cwahlmann/vz200-remake/3d-model/screenshots/monitor-v1_1.png

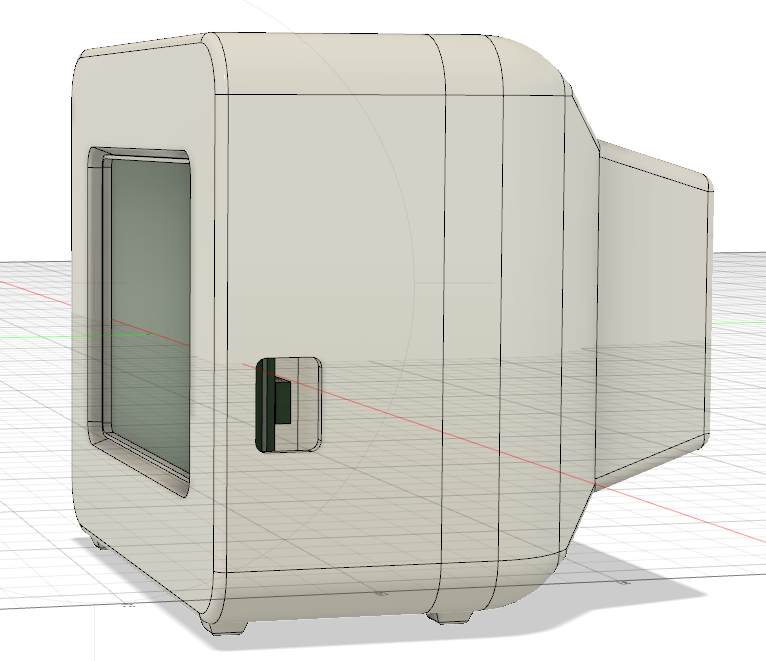
3d-model/screenshots/monitor-v1_1.png
