cwahlmann/vz200-remake/3d-model/screenshots/monitor-v1_2.png

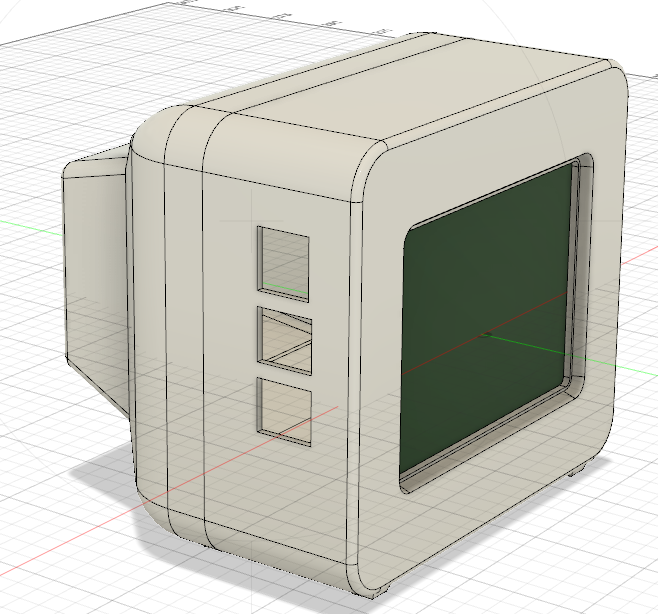
3d-model/screenshots/monitor-v1_2.png
