cwahlmann/vz200-remake/3d-model/screenshots/monitor-v1_3.png

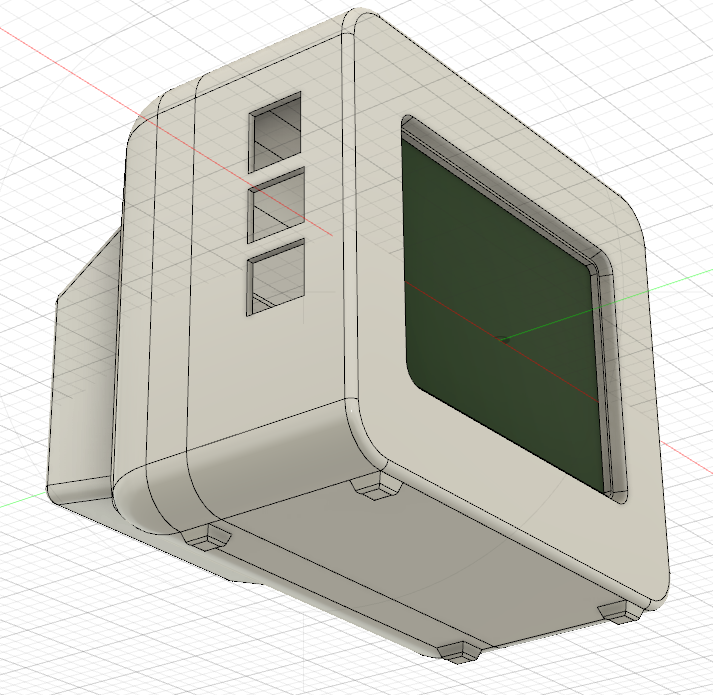
3d-model/screenshots/monitor-v1_3.png
