cwahlmann/vz200-remake/3d-model/screenshots/monitor-v2_5.png

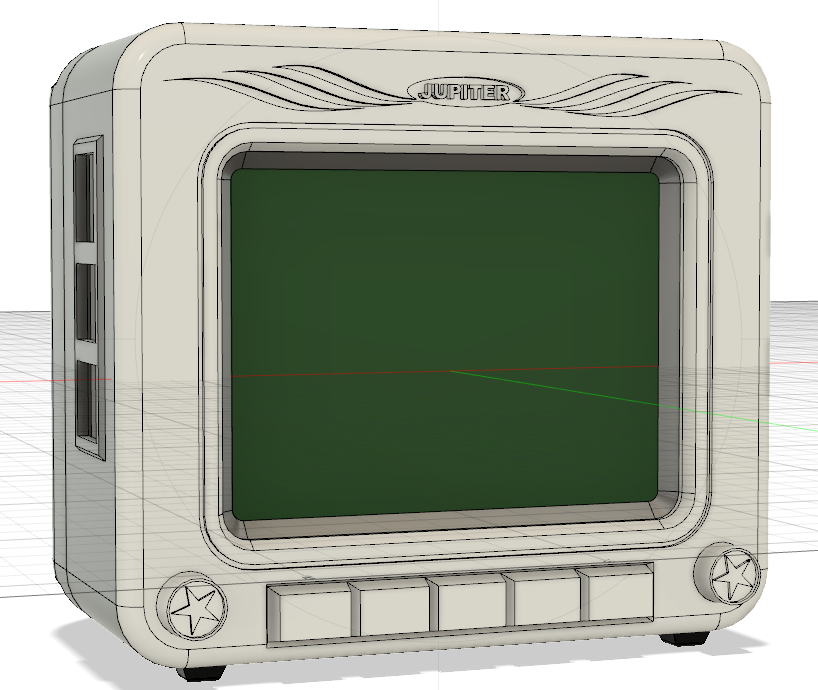
3d-model/screenshots/monitor-v2_5.png
