cwahlmann/vz200-remake/3d-model/screenshots/VZ-Fusion-0.3.png

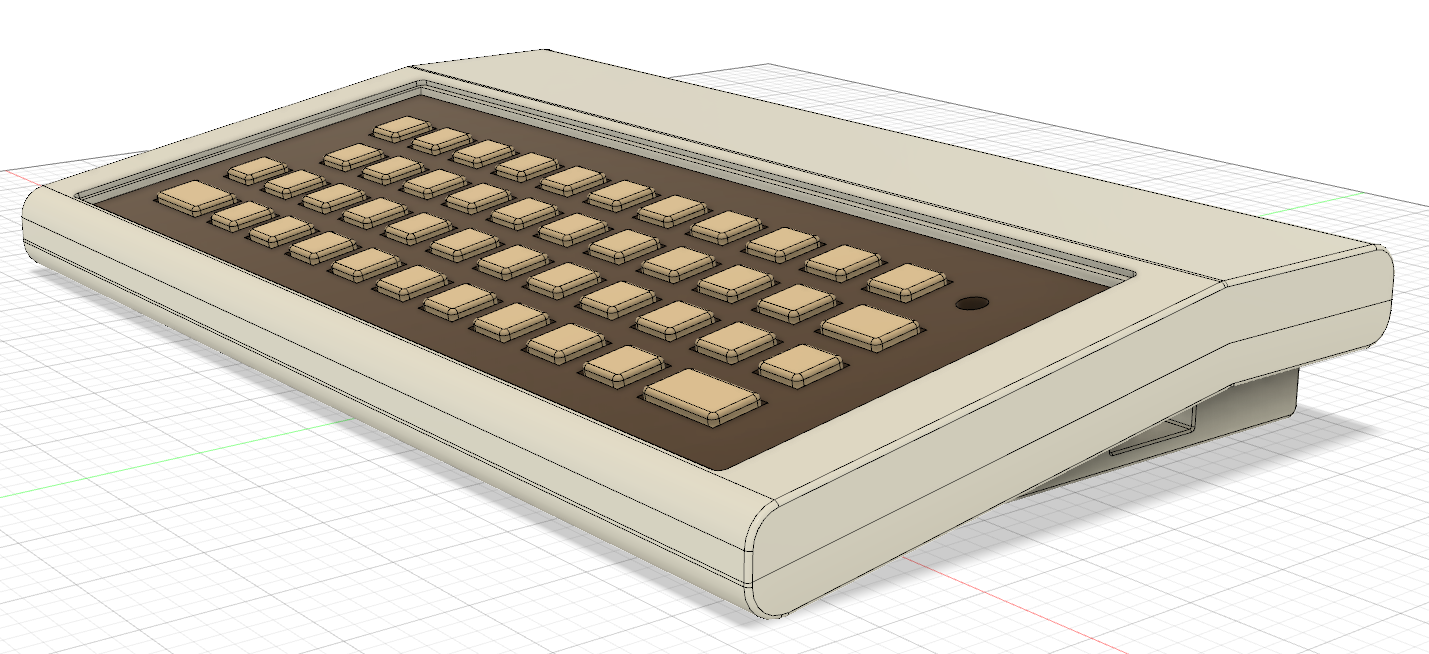
3d-model/screenshots/VZ-Fusion-0.3.png
