cwahlmann/vz200-remake/3d-model/screenshots/VZ-Fusion-0.5b.png

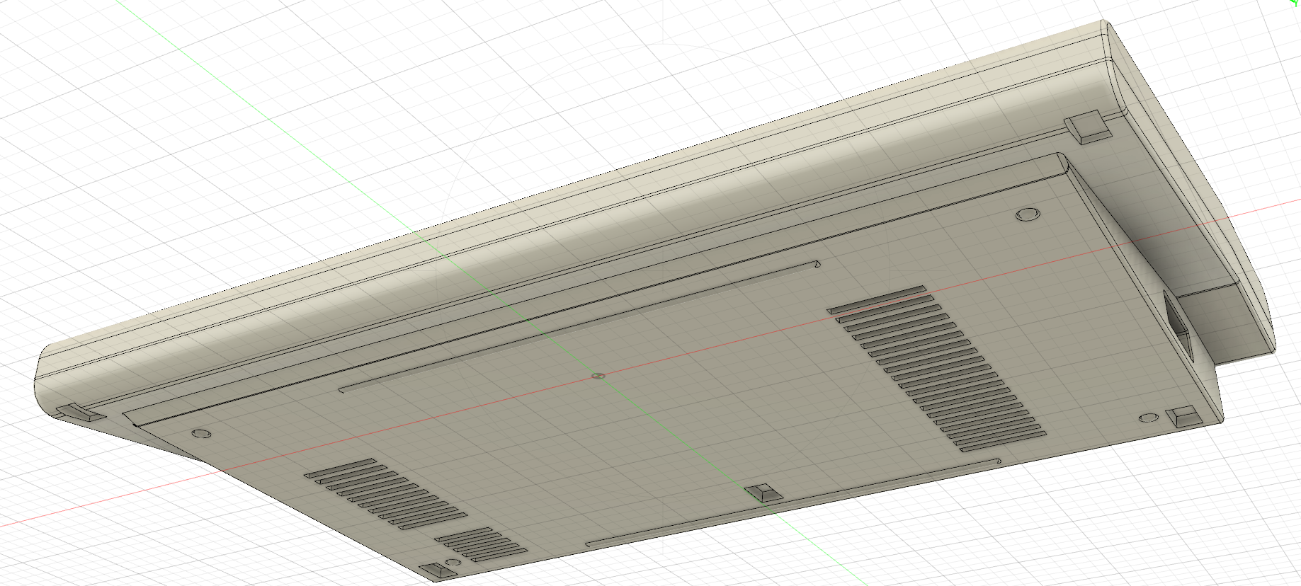
3d-model/screenshots/VZ-Fusion-0.5b.png
