cwahlmann/vz200-remake/3d-model/screenshots/VZ-Fusion-0.5c.png

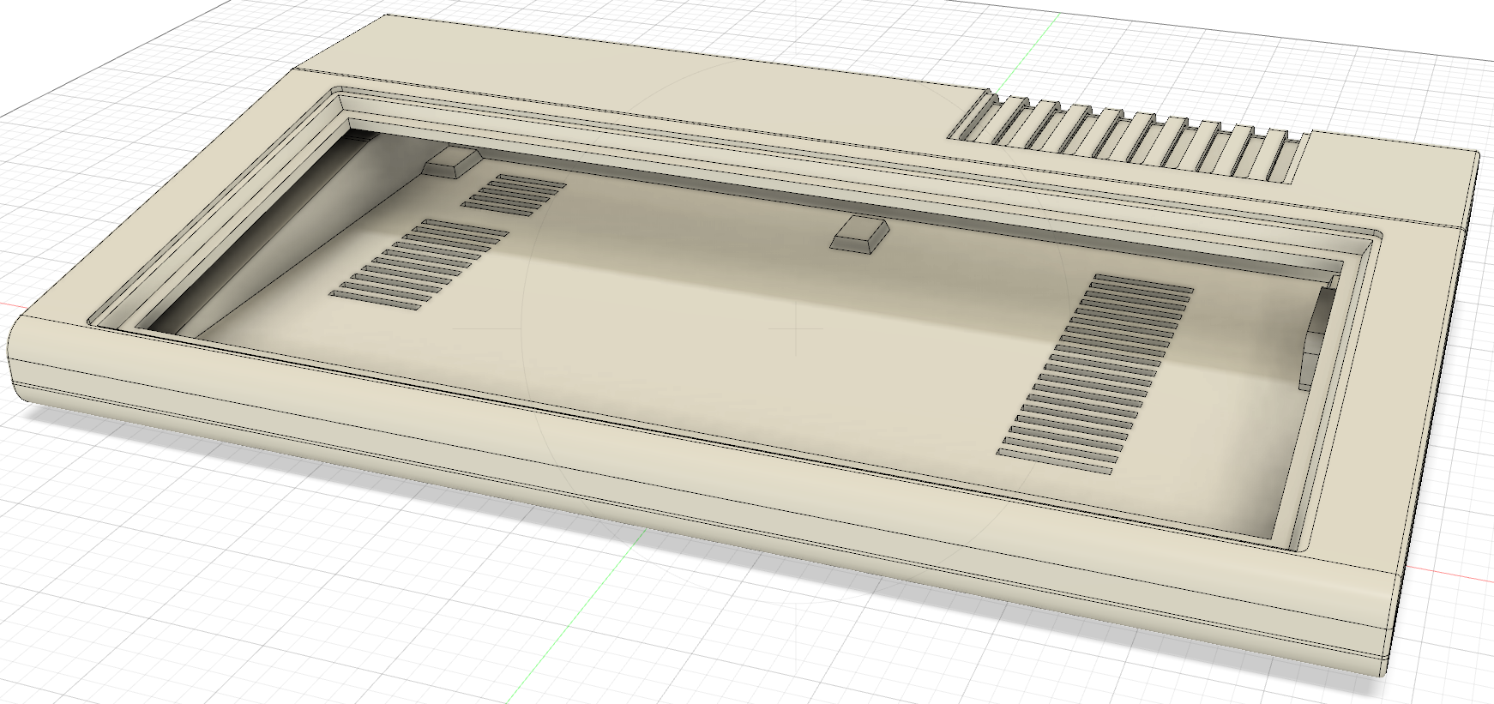
3d-model/screenshots/VZ-Fusion-0.5c.png
