cwahlmann/vz200-remake/3d-model/screenshots/VZ-Fusion-v3-Oben-hinten.png

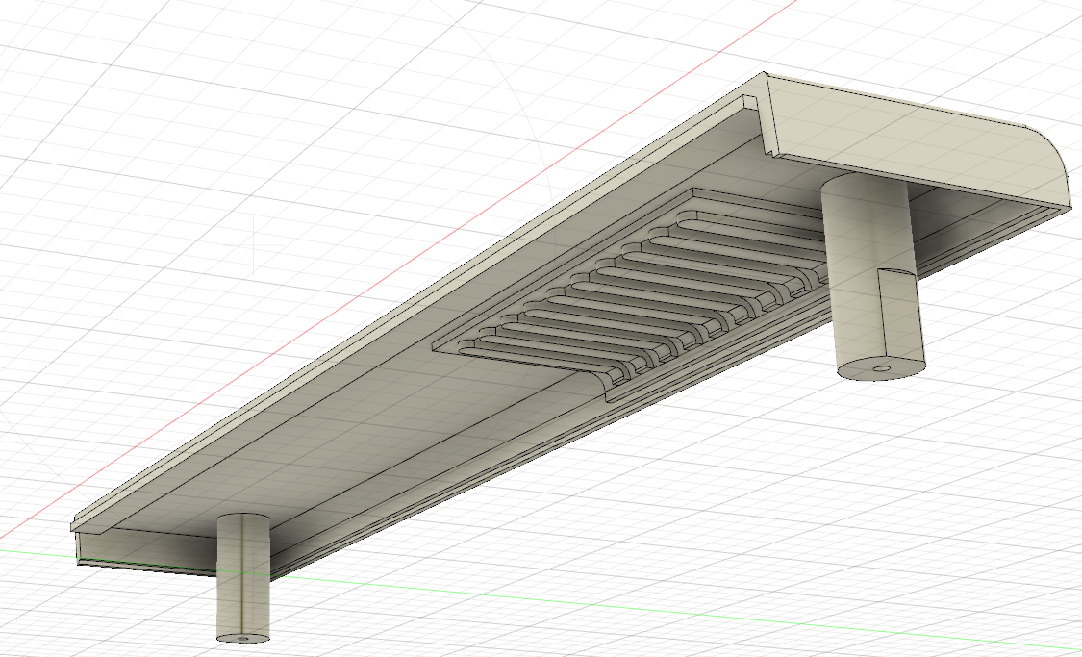
3d-model/screenshots/VZ-Fusion-v3-Oben-hinten.png
