cwahlmann/vz200-remake/3d-model/screenshots/VZ-Fusion-v3-Tastatur-Halterungen-1.png

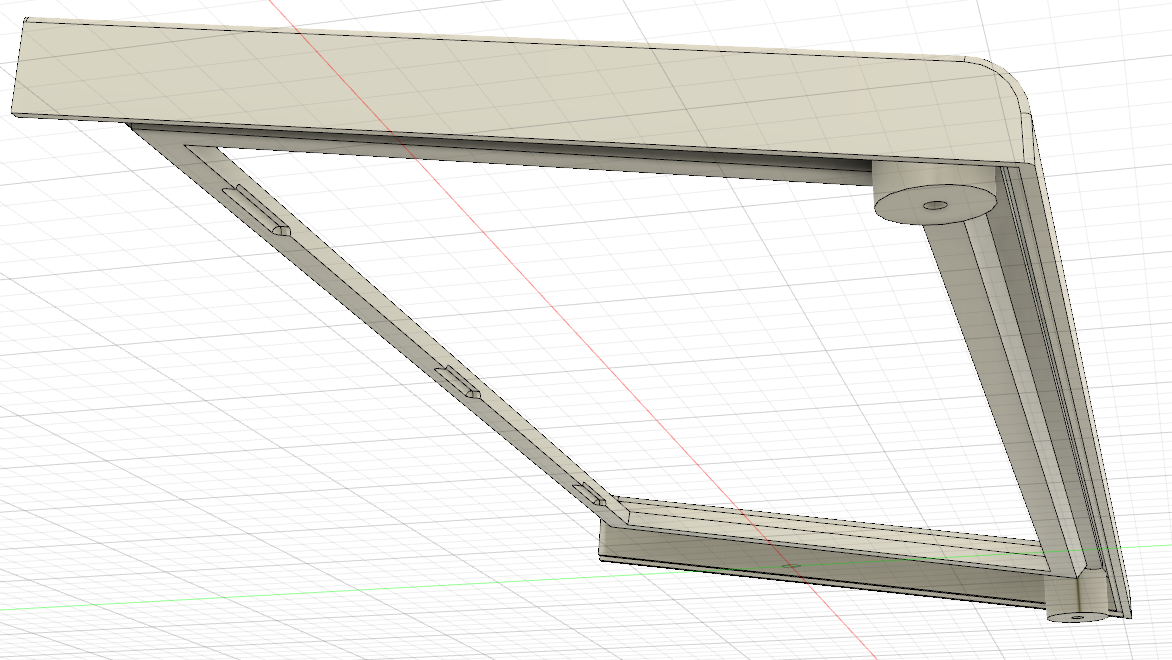
3d-model/screenshots/VZ-Fusion-v3-Tastatur-Halterungen-1.png
