cwahlmann/vz200-remake/3d-model/screenshots/VZ-Fusion-v3-Tastatur-Halterungen-3.png

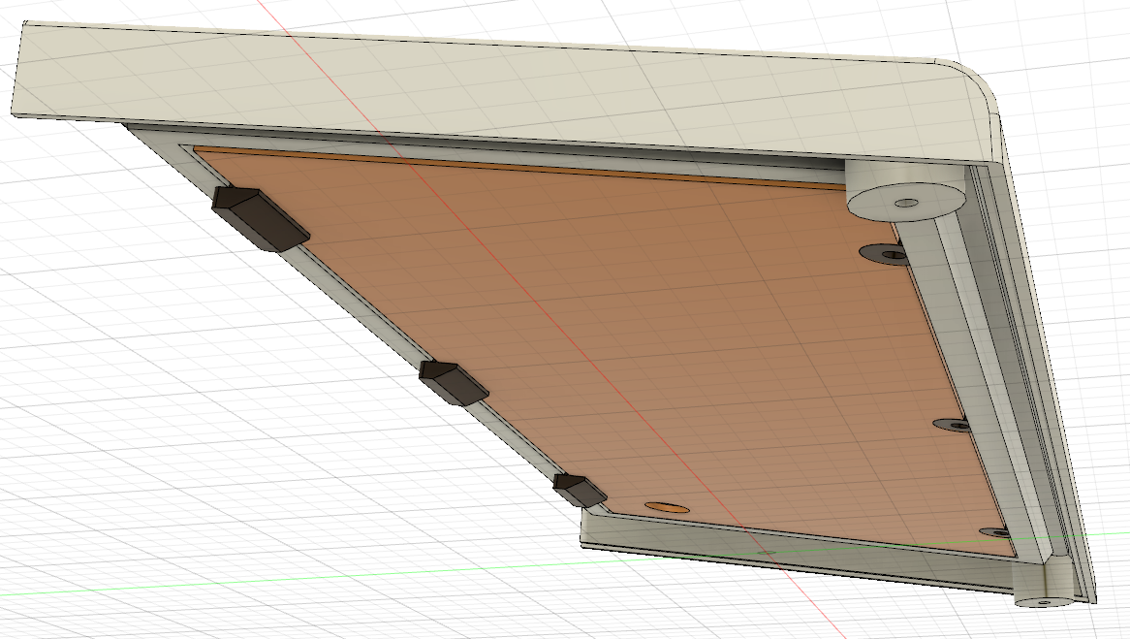
3d-model/screenshots/VZ-Fusion-v3-Tastatur-Halterungen-3.png
