cwahlmann/vz200-remake/audio/audio_schaltplan.png

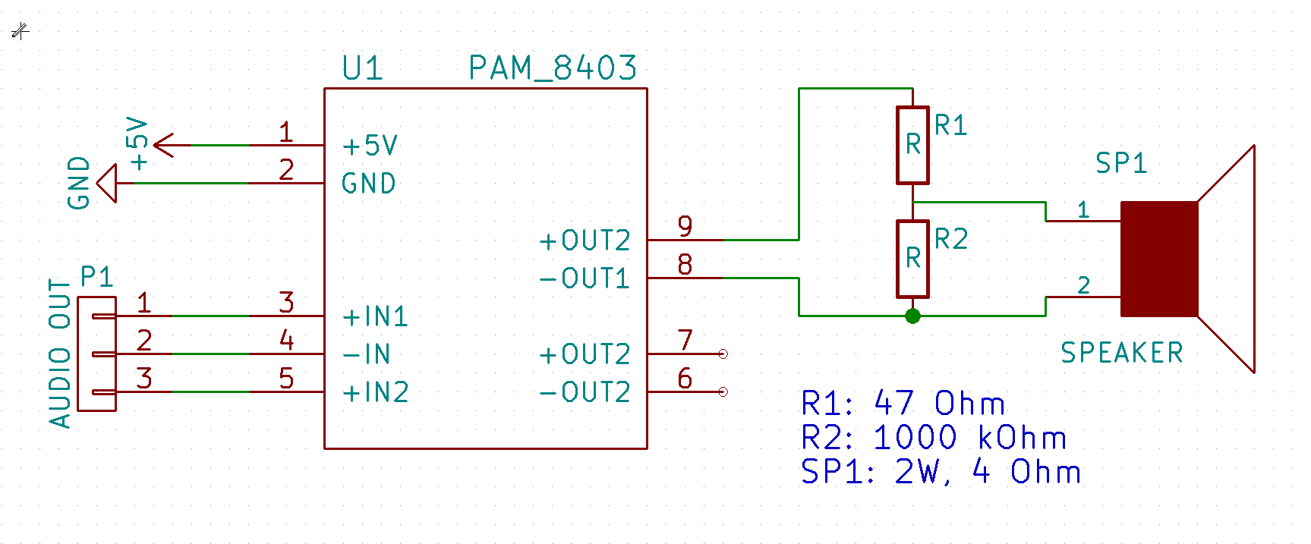
audio/audio_schaltplan.png
