cwahlmann/vz200-remake/images/3d_druck_1.jpg

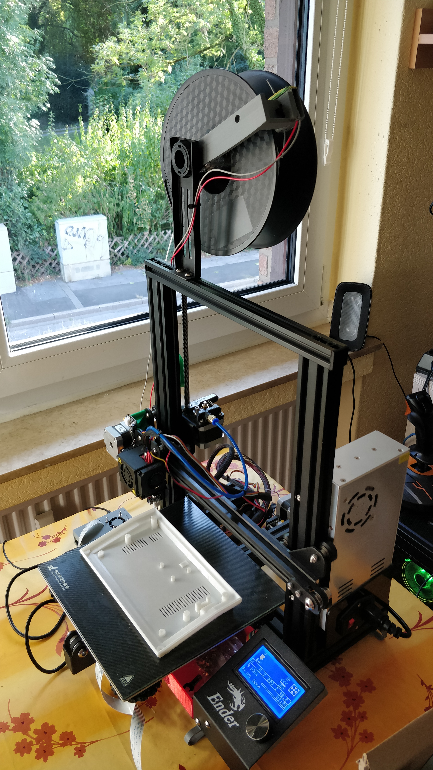
images/3d_druck_1.jpg
