cwahlmann/vz200-remake/images/3d_druck_2.jpg

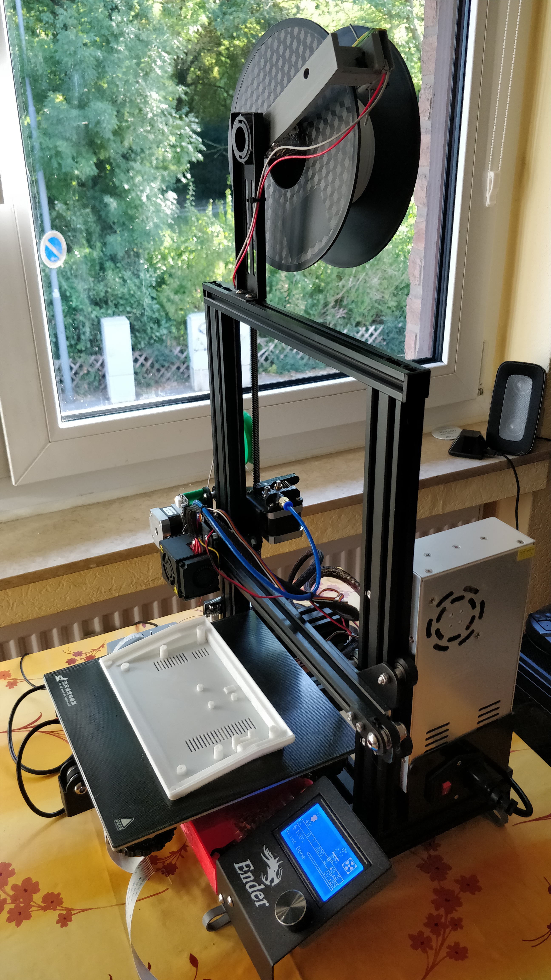
images/3d_druck_2.jpg
