cwahlmann/vz200-remake/images/img_chassis_20_platine_reset.jpg

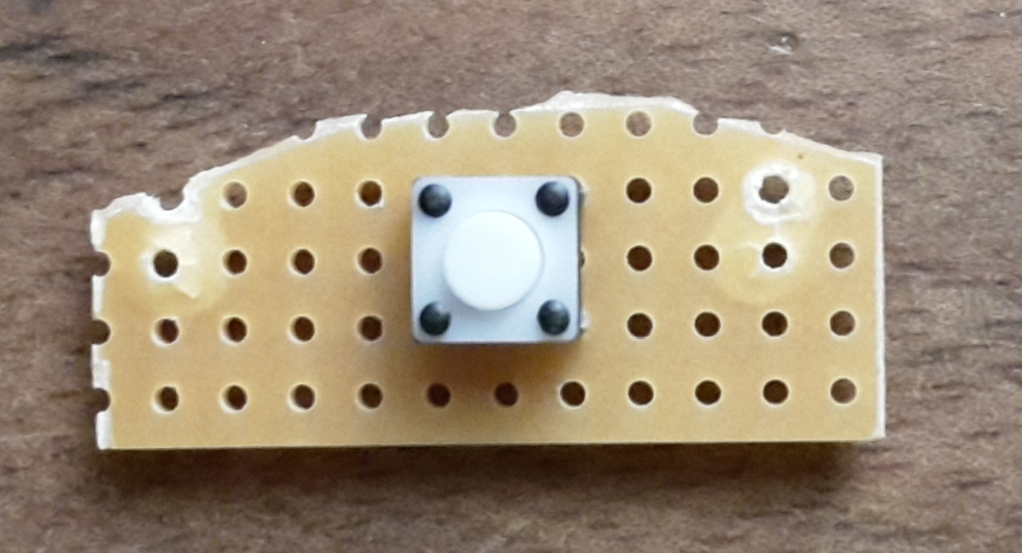
images/img_chassis_20_platine_reset.jpg
