cwahlmann/vz200-remake/images/img_chassis_23_platine_reset.jpg

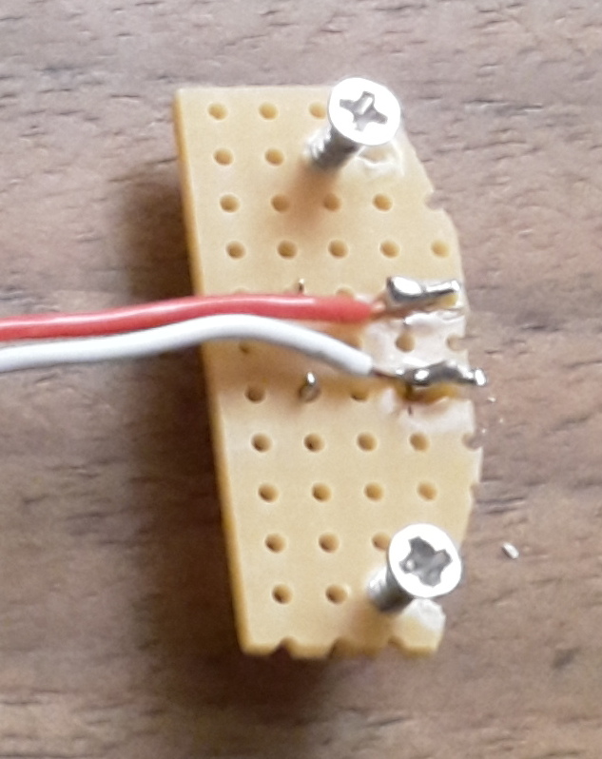
images/img_chassis_23_platine_reset.jpg
