cwahlmann/vz200-remake/images/img_monitor_15_raspberry_tft_einbau.jpg

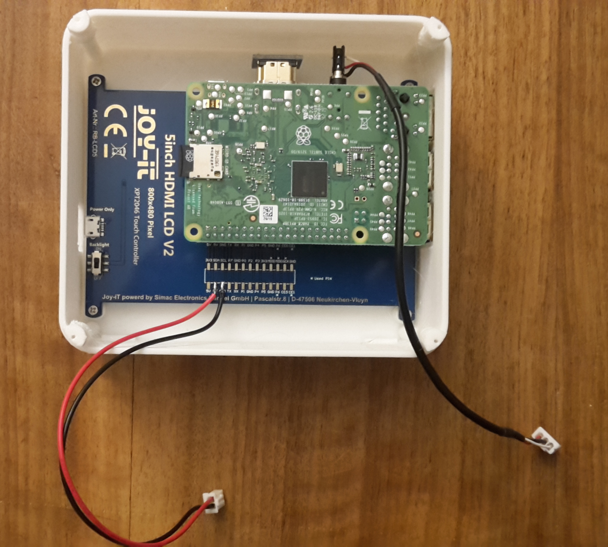
images/img_monitor_15_raspberry_tft_einbau.jpg
