cwahlmann/vz200-remake/images/img_monitor_17_verkabelung_gesamt_2.jpg

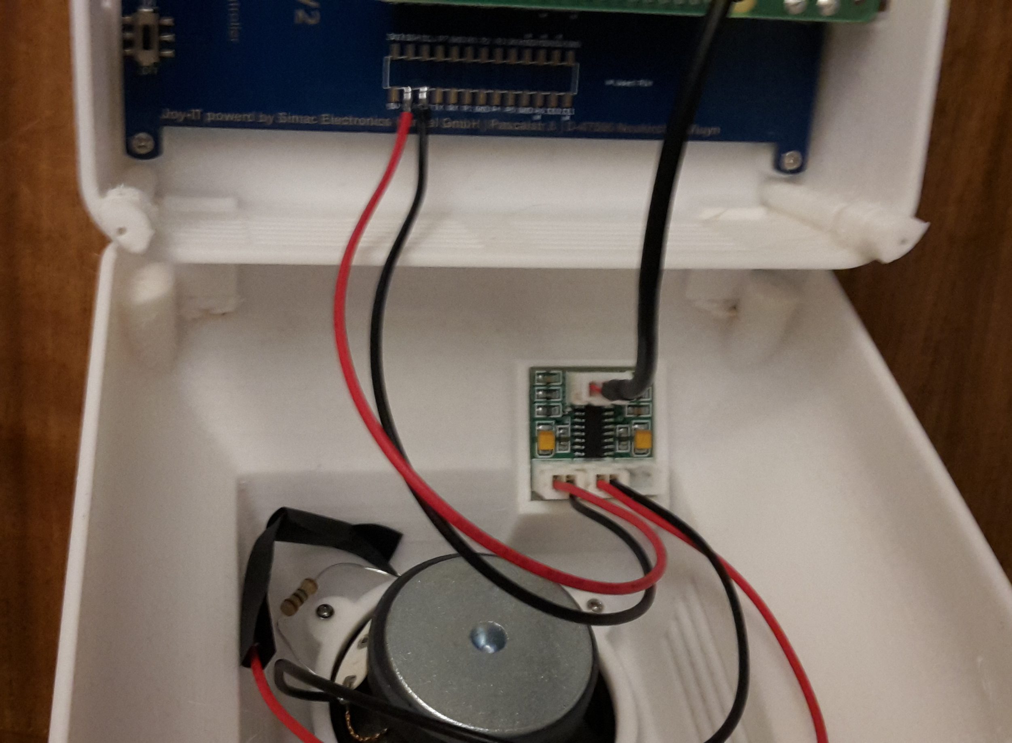
images/img_monitor_17_verkabelung_gesamt_2.jpg
