cwahlmann/vz200-remake/images/img_monitor_20_monitor_funktion.jpg

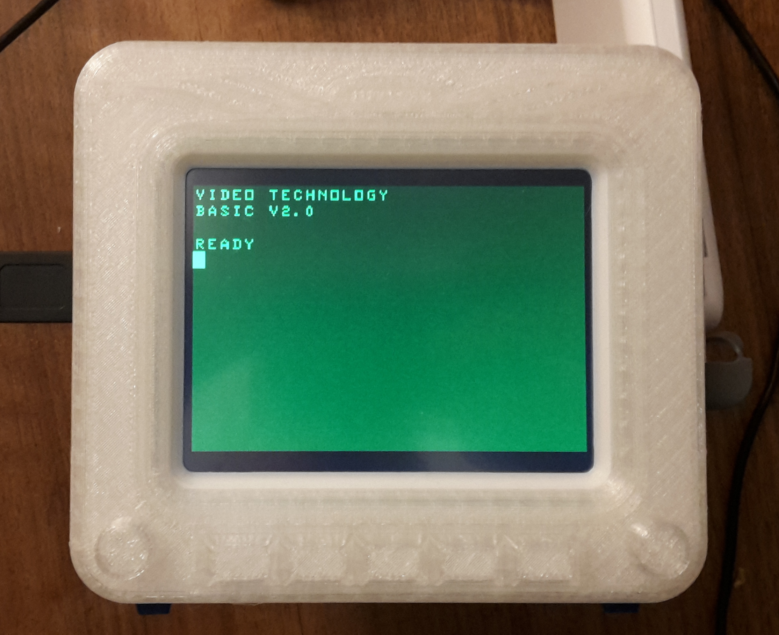
images/img_monitor_20_monitor_funktion.jpg
