cwahlmann/vz200-remake/images/render_1.png

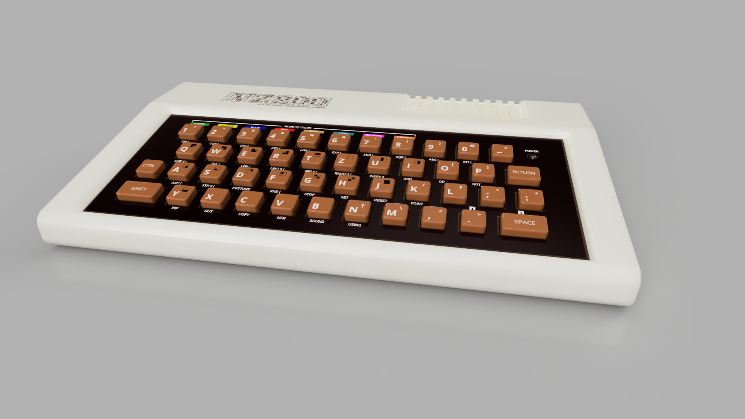
images/render_1.png
