cwahlmann/vz200-remake/images/render_2.png

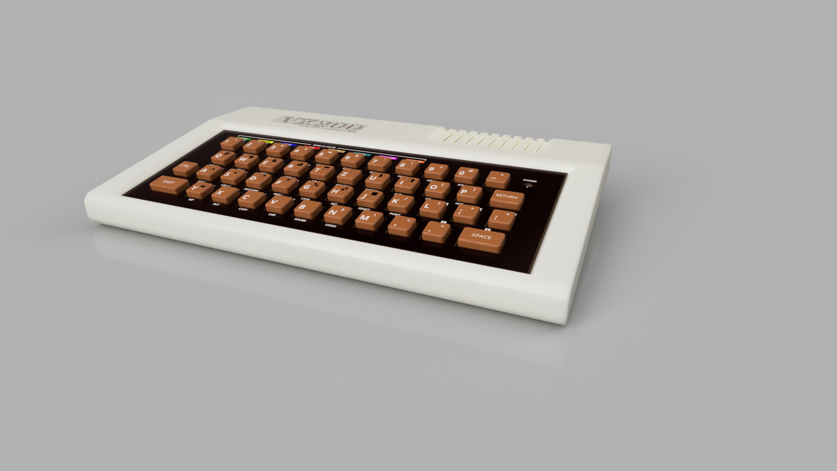
images/render_2.png
