cwahlmann/vz200-remake/images/resized/img_monitor_01_bauteile_elektrisch.jpg

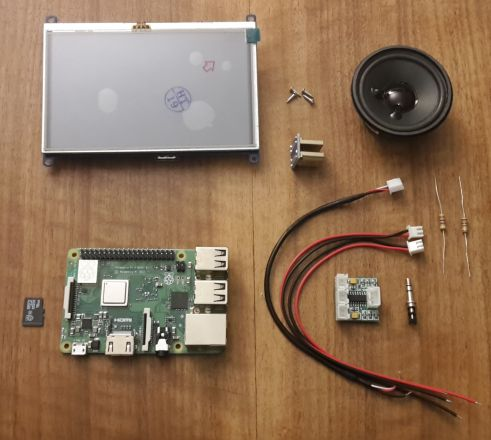
images/resized/img_monitor_01_bauteile_elektrisch.jpg
