cwahlmann/vz200-remake/images/resized/img_monitor_02_bauteile_druck.jpg

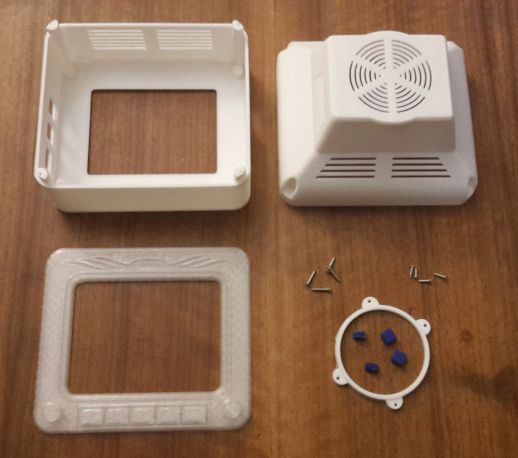
images/resized/img_monitor_02_bauteile_druck.jpg
