cwahlmann/vz200-remake/images/resized/img_monitor_03_raspberry_tft.jpg

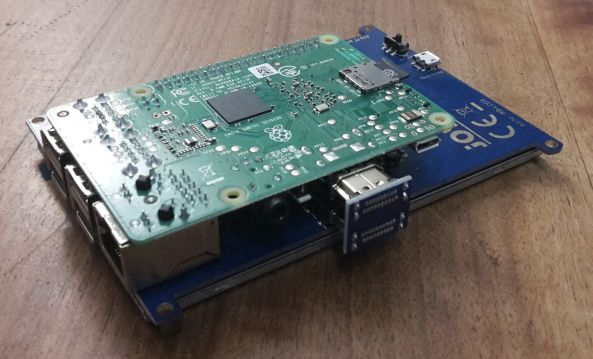
images/resized/img_monitor_03_raspberry_tft.jpg
