cwahlmann/vz200-remake/images/resized/img_monitor_04_raspberry_tft_2.jpg

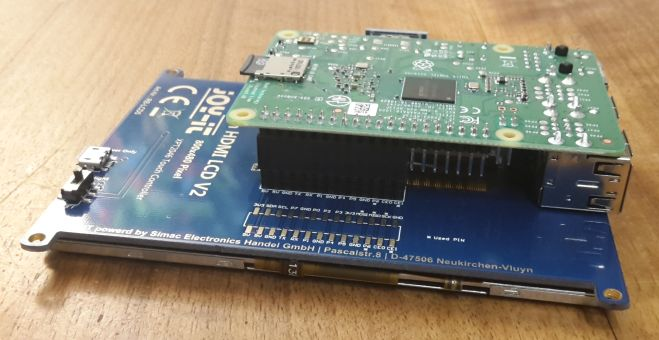
images/resized/img_monitor_04_raspberry_tft_2.jpg
