cwahlmann/vz200-remake/images/resized/img_monitor_05_speaker_spannungsteiler.jpg

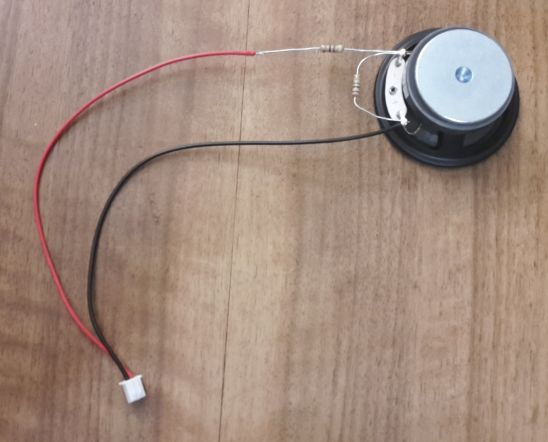
images/resized/img_monitor_05_speaker_spannungsteiler.jpg
