cwahlmann/vz200-remake/images/resized/img_monitor_06_speaker_spannungsteiler_2.jpg

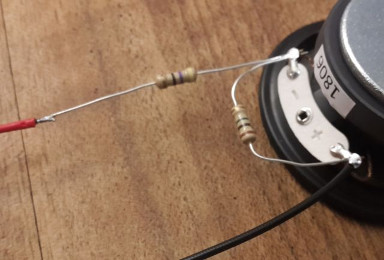
images/resized/img_monitor_06_speaker_spannungsteiler_2.jpg
