cwahlmann/vz200-remake/images/resized/img_monitor_07_klinke.jpg

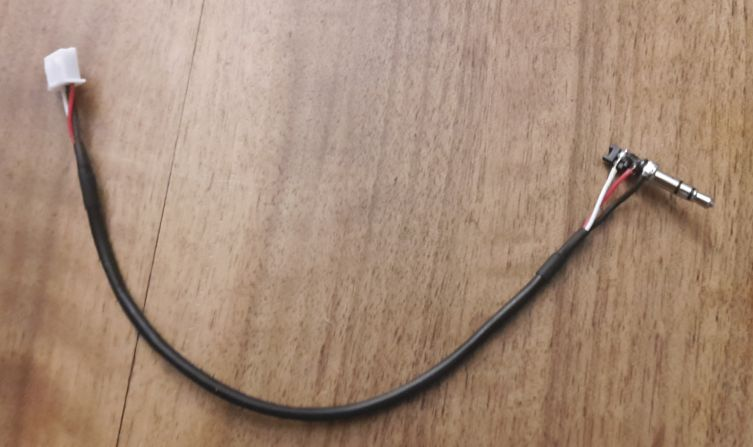
images/resized/img_monitor_07_klinke.jpg
