cwahlmann/vz200-remake/images/resized/img_monitor_08_klinke_2.jpg

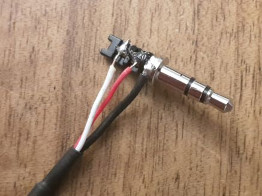
images/resized/img_monitor_08_klinke_2.jpg
