cwahlmann/vz200-remake/images/resized/img_monitor_09_audioverstärker_power.jpg

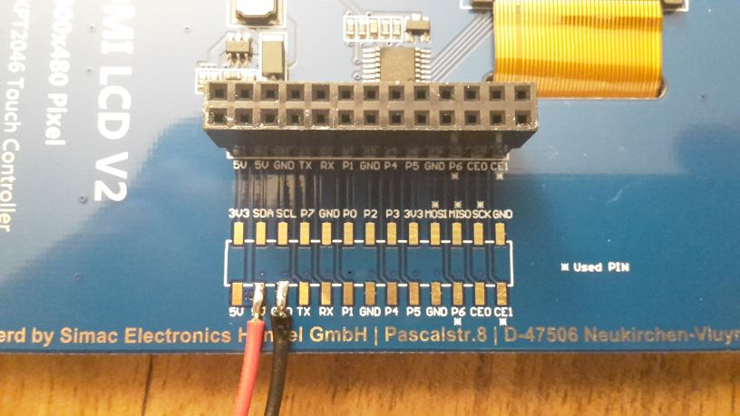
images/resized/img_monitor_09_audioverstärker_power.jpg
