cwahlmann/vz200-remake/images/resized/img_monitor_10_audioverstärker_power_2.jpg

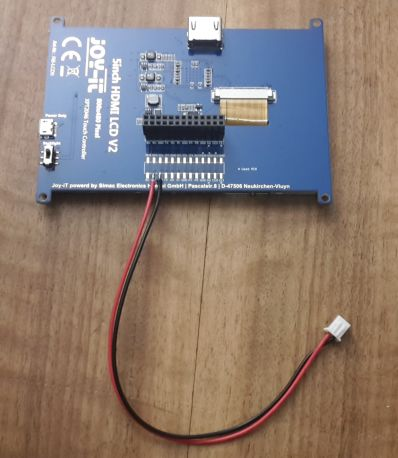
images/resized/img_monitor_10_audioverstärker_power_2.jpg
