cwahlmann/vz200-remake/images/resized/img_monitor_11_audio_gesamt.jpg

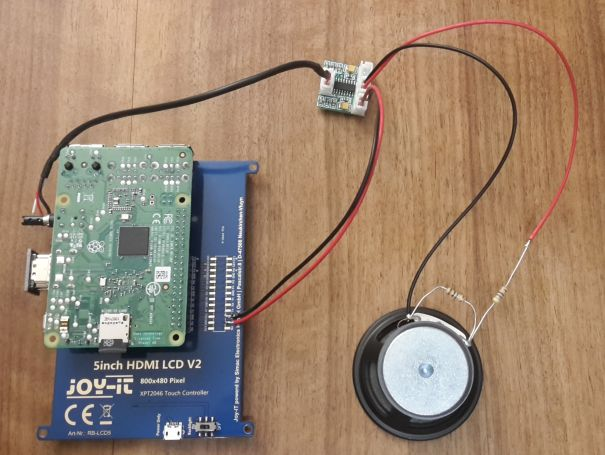
images/resized/img_monitor_11_audio_gesamt.jpg
