cwahlmann/vz200-remake/images/resized/img_monitor_12_raspberry_tft_audio_funktion.jpg

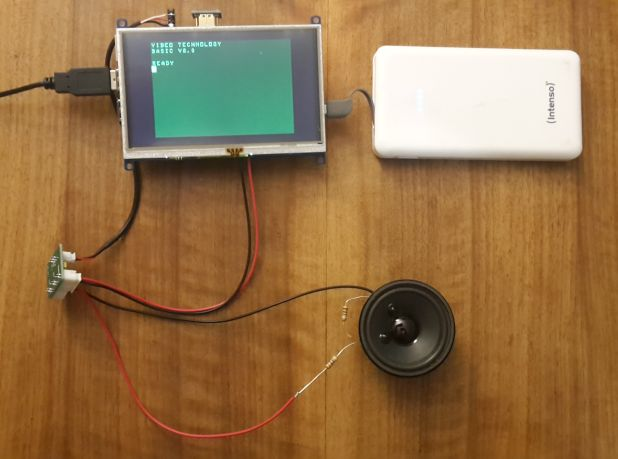
images/resized/img_monitor_12_raspberry_tft_audio_funktion.jpg
