cwahlmann/vz200-remake/images/resized/img_monitor_13_speaker_isolierung.jpg

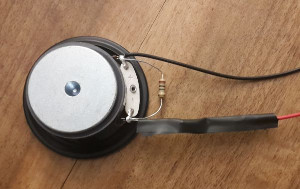
images/resized/img_monitor_13_speaker_isolierung.jpg
