cwahlmann/vz200-remake/images/resized/img_monitor_14_speaker_verstärker_einbau.jpg

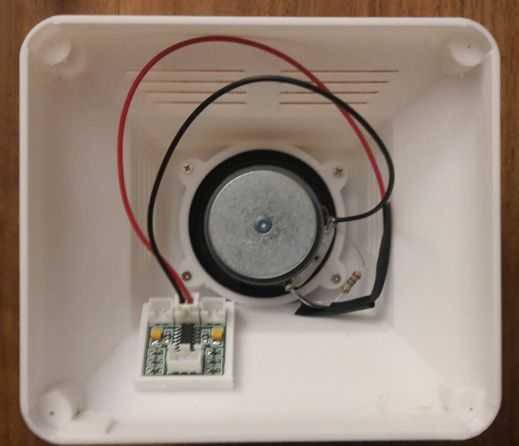
images/resized/img_monitor_14_speaker_verstärker_einbau.jpg
