cwahlmann/vz200-remake/images/resized/img_monitor_16_raspberry_tft_einbau_2.jpg

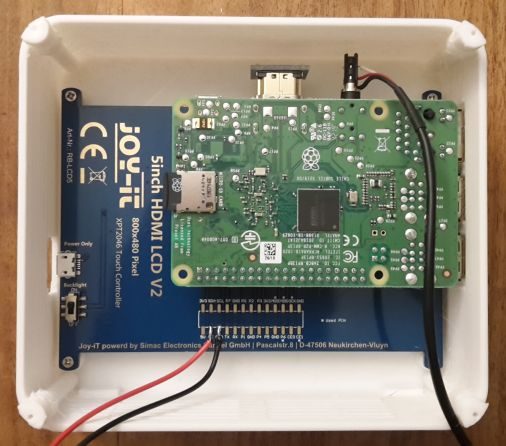
images/resized/img_monitor_16_raspberry_tft_einbau_2.jpg
