cwahlmann/vz200-remake/images/resized/img_monitor_17_verkabelung_gesamt.jpg

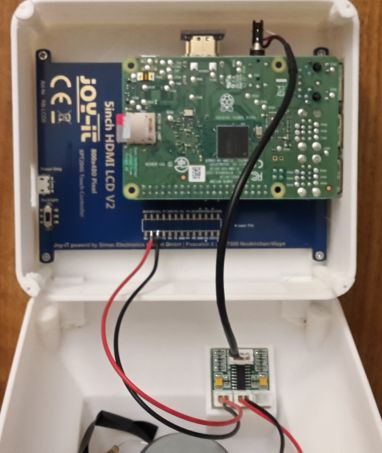
images/resized/img_monitor_17_verkabelung_gesamt.jpg
