cwahlmann/vz200-remake/images/resized/img_monitor_18_gummiüße.jpg

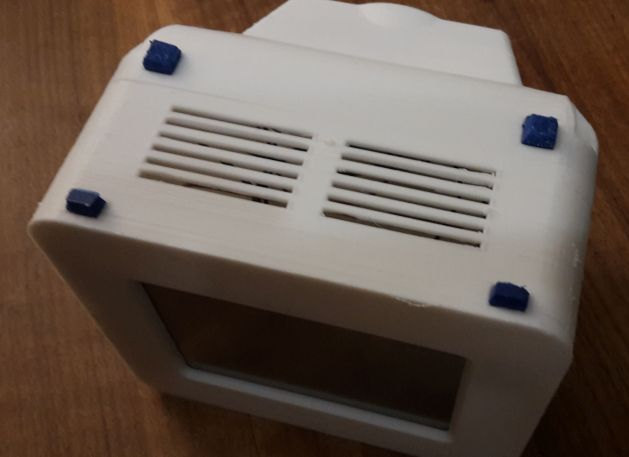
images/resized/img_monitor_18_gummiüße.jpg
