cwahlmann/vz200-remake/images/resized/img_monitor_21_monitor_front.jpg

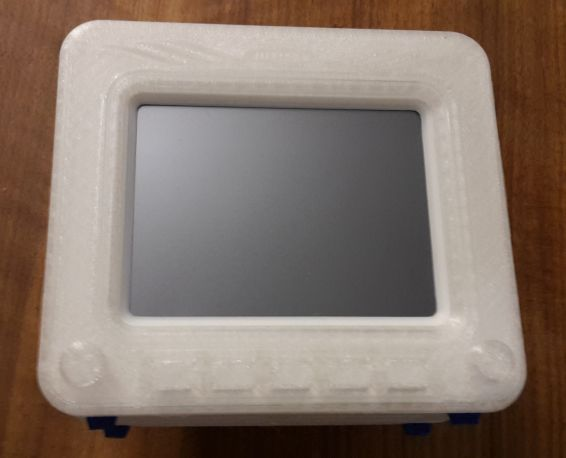
images/resized/img_monitor_21_monitor_front.jpg
