cwahlmann/vz200-remake/images/resized/img_monitor_22_monitor_bemalt.jpg

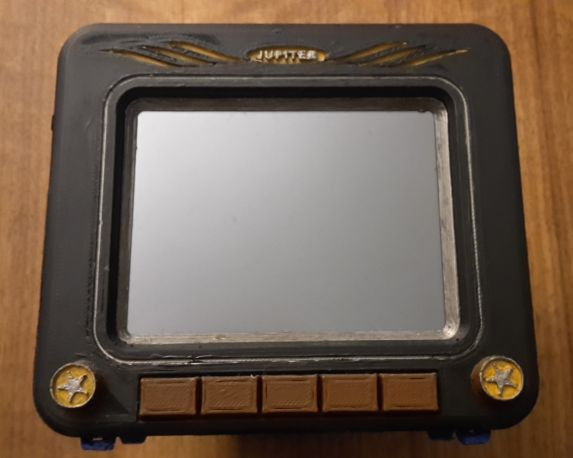
images/resized/img_monitor_22_monitor_bemalt.jpg
