cwahlmann/vz200-remake/images/vz200-social.png

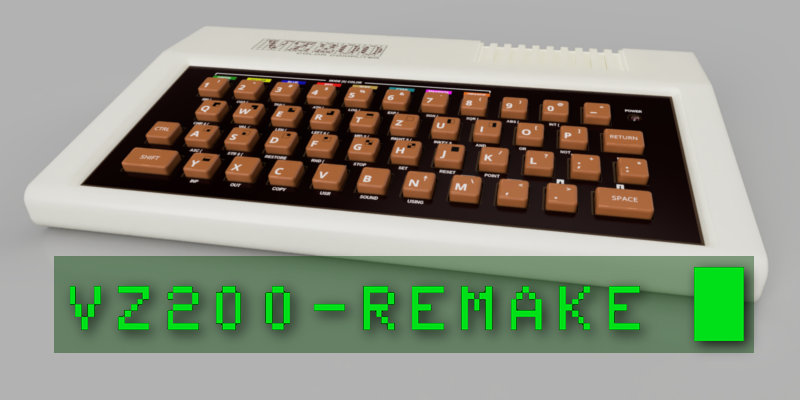
images/vz200-social.png
