cwahlmann/vz200-remake/images/vz200-social_highres.png

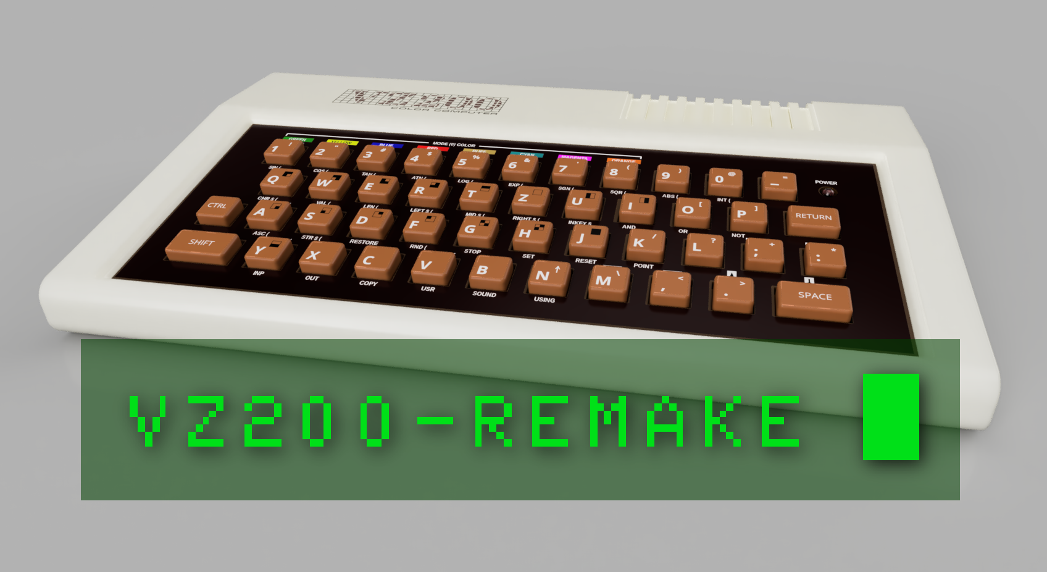
images/vz200-social_highres.png
