cwahlmann/vz200-remake/resources/aufkleber/Aufkleber-2x70perc.png

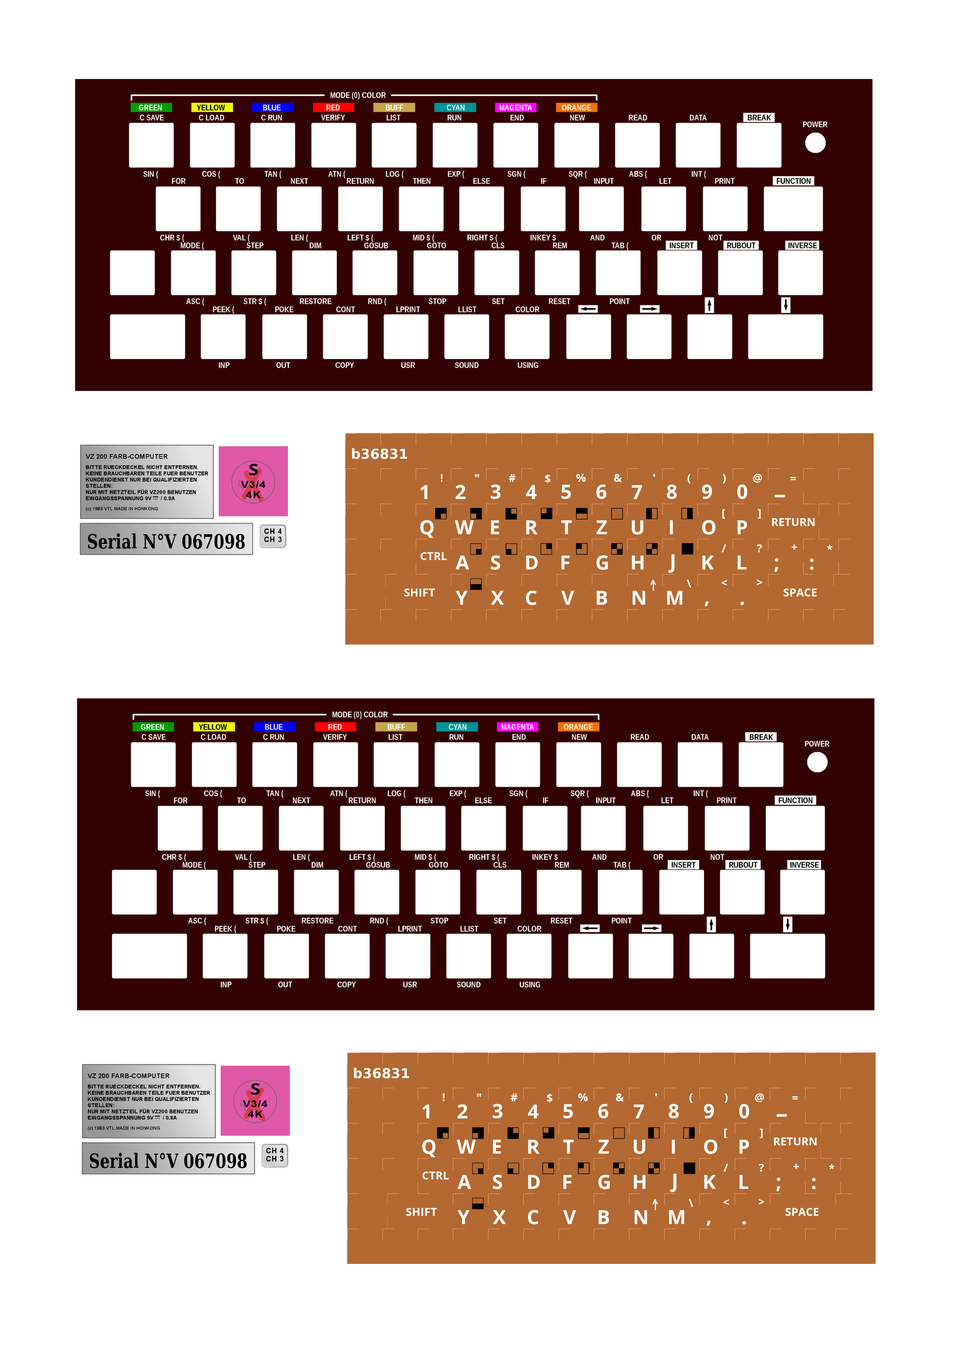
resources/aufkleber/Aufkleber-2x70perc.png
