cwahlmann/vz200-remake/tastatur/screenshots/vz200-keyboard-laypout-overlay-skizze-v1.0.png

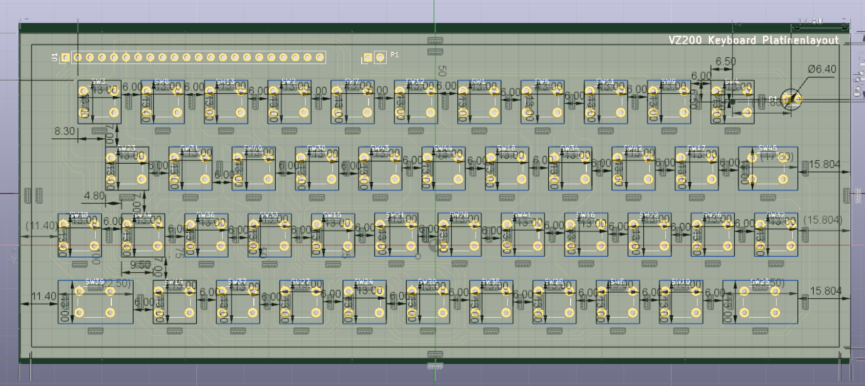
tastatur/screenshots/vz200-keyboard-laypout-overlay-skizze-v1.0.png
